emanuel36/LoRa-sensor-node-device/src/Peripheral Drivers/sx1276.c

#include <xc.h>
#include "mcu.h"
#include "sx1276.h"
#include "spi.h"

int SX1216_Inicialize(long frequency){
    RST_PIN = 0;
    RST = 0;
    __delay_ms(10);
    RST = 1;
    __delay_ms(10);

    
  // check version
  uint8_t version = readRegister(REG_VERSION);
  if (version != 0x12) {
    return 0;
  }

  // put in sleep mode
  sleep();

  // set frequency
  setFrequency(frequency);

  // set base addresses
  writeRegister(REG_FIFO_TX_BASE_ADDR, 0);
  writeRegister(REG_FIFO_RX_BASE_ADDR, 0);

  // set LNA boost
  writeRegister(REG_LNA, readRegister(REG_LNA) | 0x03);

  // set auto AGC
  writeRegister(REG_MODEM_CONFIG_3, 0x04);

  // set output power to 17 dBm
  setTxPower(17, PA_OUTPUT_PA_BOOST_PIN);

  // put in standby mode
  idle();

  return 1;
}

uint8_t readRegister(uint8_t address)
{
  return singleTransfer(address & 0x7f, 0x00);
}

void sleep()
{
  writeRegister(REG_OP_MODE, MODE_LONG_RANGE_MODE | MODE_SLEEP);
}

void setFrequency(long frequency)
{
  //_frequency = frequency;

  //uint64_t frf = ((uint64_t)frequency << 19) / 32000000;

    uint32_t frf = 14991360;
    
  writeRegister(REG_FRF_MSB, (uint8_t)(frf >> 16));
  writeRegister(REG_FRF_MID, (uint8_t)(frf >> 8));
  writeRegister(REG_FRF_LSB, (uint8_t)(frf >> 0));
}

void writeRegister(uint8_t address, uint8_t value)
{
  singleTransfer(address | 0x80, value);
}

void setTxPower(int level, int outputPin)
{
  if (PA_OUTPUT_RFO_PIN == outputPin) {
    // RFO
    if (level < 0) {
      level = 0;
    } else if (level > 14) {
      level = 14;
    }

    writeRegister(REG_PA_CONFIG, 0x70 | level);
  } else {
    // PA BOOST
    if (level > 17) {
      if (level > 20) {
        level = 20;
      }

      // subtract 3 from level, so 18 - 20 maps to 15 - 17
      level -= 3;

      // High Power +20 dBm Operation (Semtech SX1276/77/78/79 5.4.3.)
      writeRegister(REG_PA_DAC, 0x87);
      setOCP(140);
    } else {
      if (level < 2) {
        level = 2;
      }
      //Default value PA_HF/LF or +17dBm
      writeRegister(REG_PA_DAC, 0x84);
      setOCP(100);
    }

    writeRegister(REG_PA_CONFIG, PA_BOOST | (level - 2));
  }
}

void idle()
{
  writeRegister(REG_OP_MODE, MODE_LONG_RANGE_MODE | MODE_STDBY);
}

uint8_t singleTransfer(uint8_t address, uint8_t value)
{
  uint8_t response;

  chipEnable();

  SPI2_Exchange8bit(address);
  response = SPI2_Exchange8bit(value);

  chipDisable();

  return response;
}

void setOCP(uint8_t mA)
{
  uint8_t ocpTrim = 27;

  if (mA <= 120) {
    ocpTrim = (mA - 45) / 5;
  } else if (mA <=240) {
    ocpTrim = (mA + 30) / 10;
  }

  writeRegister(REG_OCP, 0x20 | (0x1F & ocpTrim));
}

int beginPacket(int implicitHeader){
  if (isTransmitting()) {
    return 0;
  }

  // put in standby mode
  idle();

  if (implicitHeader) {
    implicitHeaderMode();
  } else {
    explicitHeaderMode();
  }

  // reset FIFO address and paload length
  writeRegister(REG_FIFO_ADDR_PTR, 0);
  writeRegister(REG_PAYLOAD_LENGTH, 0);

  return 1;
}

bool isTransmitting(){
  if ((readRegister(REG_OP_MODE) & MODE_TX) == MODE_TX) {
    return true;
  }

  if (readRegister(REG_IRQ_FLAGS) & IRQ_TX_DONE_MASK) {
    // clear IRQ's
    writeRegister(REG_IRQ_FLAGS, IRQ_TX_DONE_MASK);
  }

  return false;
}

void explicitHeaderMode(){
  //_implicitHeaderMode = 0;

  writeRegister(REG_MODEM_CONFIG_1, readRegister(REG_MODEM_CONFIG_1) & 0xfe);
}

void implicitHeaderMode(){
  //_implicitHeaderMode = 1;

  writeRegister(REG_MODEM_CONFIG_1, readRegister(REG_MODEM_CONFIG_1) | 0x01);
}

void SX1276WriteString(char *string){
    while(*string != '\0'){
        writeByte(*string);
        string++;
    }
}

unsigned writeByte(uint8_t byte)
{
  return write(&byte, sizeof(byte));
}

unsigned write(const uint8_t *buffer, unsigned size)
{
  int currentLength = readRegister(REG_PAYLOAD_LENGTH);

  // check size
  if ((currentLength + size) > MAX_PKT_LENGTH) {
    size = MAX_PKT_LENGTH - currentLength;
  }

  // write data
  for (unsigned i = 0; i < size; i++) {
    writeRegister(REG_FIFO, buffer[i]);
  }

  // update length
  writeRegister(REG_PAYLOAD_LENGTH, currentLength + size);

  return size;
}

int endPacket(bool async)
{
  // put in TX mode
  writeRegister(REG_OP_MODE, MODE_LONG_RANGE_MODE | MODE_TX);

  if (async) {
    // grace time is required for the radio
    __delay_us(150);
  } else {
    // wait for TX done
    while ((readRegister(REG_IRQ_FLAGS) & IRQ_TX_DONE_MASK) == 0) {
      //yield();
    }
    // clear IRQ's
    writeRegister(REG_IRQ_FLAGS, IRQ_TX_DONE_MASK);
  }

  return 1;
}
