emanuel36/LoRa-sensor-node-device/src/Peripheral Drivers/ds18b20.c

#include "ds18b20.h"
#include "oneWire.h"

void ds18b20Setup(){
    OneWireReset(); // Reset Pulse 
    OneWireWriteByte(0xCC); // Issue skip ROM command (CCh)
    OneWireWriteByte(0x44); // Convert T command (44h)
    while(!BUSIN); // DS will hold line low while making measurement
    OneWireReset(); // Start new command sequence 
    OneWireWriteByte(0xCC); // Issue skip ROM command 
    OneWireWriteByte(0xBE); // Read Scratchpad (BEh) - 15 bits
    OneWireReadByte();
    OneWireReadByte();
    OneWireReset(); // Stop Reading 
}

void ds18b20Read(float *temp){
    OneWireReset(); // Reset Pulse 
    OneWireWriteByte(0xCC); // Issue skip ROM command (CCh)
    OneWireWriteByte(0x44); // Convert T command (44h)
    while(!BUSIN); // DS will hold line low while making measurement
    OneWireReset(); // Start new command sequence 
    OneWireWriteByte(0xCC); // Issue skip ROM command 
    OneWireWriteByte(0xBE); // Read Scratchpad (BEh) - 15 bits
    unsigned char LSB = OneWireReadByte();
    unsigned char MSB = OneWireReadByte();
    OneWireReset(); // Stop Reading 
    unsigned int data = MSB;
    float temperature = (data << 8) | LSB;
    *temp = temperature/16; //temperature in celcius
}
